collin80/TeslaBMS/Logger.cpp

/*
 * Logger.cpp
 *
 Copyright (c) 2013 Collin Kidder, Michael Neuweiler, Charles Galpin

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
 */

#include "Logger.h"

Logger::LogLevel Logger::logLevel = Logger::Info;
uint32_t Logger::lastLogTime = 0;

/*
 * Output a debug message with a variable amount of parameters.
 * printf() style, see Logger::log()
 *
 */
void Logger::debug(char *message, ...) {
    if (logLevel > Debug)
        return;
    va_list args;
    va_start(args, message);
    Logger::log(Debug, message, args);
    va_end(args);
}

/*
 * Output a info message with a variable amount of parameters
 * printf() style, see Logger::log()
 */
void Logger::info(char *message, ...) {
    if (logLevel > Info)
        return;
    va_list args;
    va_start(args, message);
    Logger::log(Info, message, args);
    va_end(args);
}

/*
 * Output a warning message with a variable amount of parameters
 * printf() style, see Logger::log()
 */
void Logger::warn(char *message, ...) {
    if (logLevel > Warn)
        return;
    va_list args;
    va_start(args, message);
    Logger::log(Warn, message, args);
    va_end(args);
}

/*
 * Output a error message with a variable amount of parameters
 * printf() style, see Logger::log()
 */
void Logger::error(char *message, ...) {
    if (logLevel > Error)
        return;
    va_list args;
    va_start(args, message);
    Logger::log(Error, message, args);
    va_end(args);
}

/*
 * Output a comnsole message with a variable amount of parameters
 * printf() style, see Logger::logMessage()
 */
void Logger::console(char *message, ...) {
    va_list args;
    va_start(args, message);
    Logger::logMessage(message, args);
    va_end(args);
}

/*
 * Set the log level. Any output below the specified log level will be omitted.
 */
void Logger::setLoglevel(LogLevel level) {
    logLevel = level;
}

/*
 * Retrieve the current log level.
 */
Logger::LogLevel Logger::getLogLevel() {
    return logLevel;
}

/*
 * Return a timestamp when the last log entry was made.
 */
uint32_t Logger::getLastLogTime() {
    return lastLogTime;
}

/*
 * Returns if debug log level is enabled. This can be used in time critical
 * situations to prevent unnecessary string concatenation (if the message won't
 * be logged in the end).
 *
 * Example:
 * if (Logger::isDebug()) {
 *    Logger::debug("current time: %d", millis());
 * }
 */
boolean Logger::isDebug() {
    return logLevel == Debug;
}

/*
 * Output a log message (called by debug(), info(), warn(), error(), console())
 *
 * Supports printf() like syntax:
 *
 * %% - outputs a '%' character
 * %s - prints the next parameter as string
 * %d - prints the next parameter as decimal
 * %f - prints the next parameter as double float
 * %x - prints the next parameter as hex value
 * %X - prints the next parameter as hex value with '0x' added before
 * %b - prints the next parameter as binary value
 * %B - prints the next parameter as binary value with '0b' added before
 * %l - prints the next parameter as long
 * %c - prints the next parameter as a character
 * %t - prints the next parameter as boolean ('T' or 'F')
 * %T - prints the next parameter as boolean ('true' or 'false')
 */
void Logger::log(LogLevel level, char *format, va_list args) {
    lastLogTime = millis();
    SERIALCONSOLE.print(lastLogTime);
    SERIALCONSOLE.print(" - ");

    switch (level) {
    case Debug:
        SERIALCONSOLE.print("DEBUG");
        break;
    case Info:
        SERIALCONSOLE.print("INFO");
        break;
    case Warn:
        SERIALCONSOLE.print("WARNING");
        break;
    case Error:
        SERIALCONSOLE.print("ERROR");
        break;
    }
    SERIALCONSOLE.print(": ");

    logMessage(format, args);
}

/*
 * Output a log message (called by log(), console())
 *
 * Supports printf() like syntax:
 *
 * %% - outputs a '%' character
 * %s - prints the next parameter as string
 * %d - prints the next parameter as decimal
 * %f - prints the next parameter as double float
 * %x - prints the next parameter as hex value
 * %X - prints the next parameter as hex value with '0x' added before
 * %b - prints the next parameter as binary value
 * %B - prints the next parameter as binary value with '0b' added before
 * %l - prints the next parameter as long
 * %c - prints the next parameter as a character
 * %t - prints the next parameter as boolean ('T' or 'F')
 * %T - prints the next parameter as boolean ('true' or 'false')
 */
void Logger::logMessage(char *format, va_list args) {
    for (; *format != 0; ++format) {
        if (*format == '%') {
            ++format;
            if (*format == '\0')
                break;
            if (*format == '%') {
                SERIALCONSOLE.print(*format);
                continue;
            }
            if (*format == 's') {
                register char *s = (char *) va_arg( args, int );
                SERIALCONSOLE.print(s);
                continue;
            }
            if (*format == 'd' || *format == 'i') {
                SERIALCONSOLE.print(va_arg( args, int ), DEC);
                continue;
            }
            if (*format == 'f') {
                SERIALCONSOLE.print(va_arg( args, double ), 3);
                continue;
            }
            if (*format == 'x') {
                SERIALCONSOLE.print(va_arg( args, int ), HEX);
                continue;
            }
            if (*format == 'X') {
                SERIALCONSOLE.print("0x");
                SERIALCONSOLE.print(va_arg( args, int ), HEX);
                continue;
            }
            if (*format == 'b') {
                SERIALCONSOLE.print(va_arg( args, int ), BIN);
                continue;
            }
            if (*format == 'B') {
                SERIALCONSOLE.print("0b");
                SERIALCONSOLE.print(va_arg( args, int ), BIN);
                continue;
            }
            if (*format == 'l') {
                SERIALCONSOLE.print(va_arg( args, long ), DEC);
                continue;
            }

            if (*format == 'c') {
                SERIALCONSOLE.print(va_arg( args, int ));
                continue;
            }
            if (*format == 't') {
                if (va_arg( args, int ) == 1) {
                    SERIALCONSOLE.print("T");
                } else {
                    SERIALCONSOLE.print("F");
                }
                continue;
            }
            if (*format == 'T') {
                if (va_arg( args, int ) == 1) {
                    SERIALCONSOLE.print("TRUE");
                } else {
                    SERIALCONSOLE.print("FALSE");
                }
                continue;
            }

        }
        SERIALCONSOLE.print(*format);
    }
    SERIALCONSOLE.println();
}
